Cyril-vsr/Capteur_Gaz/fichier LT Spice/New_Symbol.asc

B1: bi; I=V(cp,cn)*({G0}+{G1}*V(gc,gn))
C1: cap; 200µ
R1: res; 1k
Named nets: cp, cn, gp, gc, gn
